Gearhead145/piled/Component Datasheets/PILED/113_0601/IMGP3079.JPG

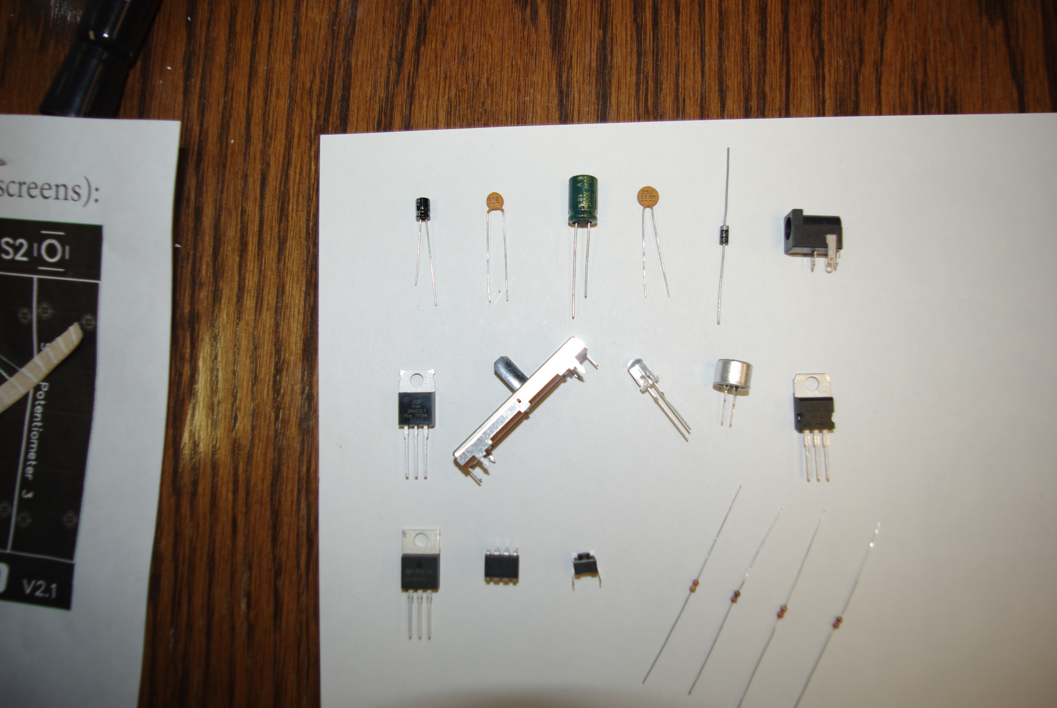
Component Datasheets/PILED/113_0601/IMGP3079.JPG
