Gearhead145/piled/Component Datasheets/PILED/113_0601/IMGP3086.JPG

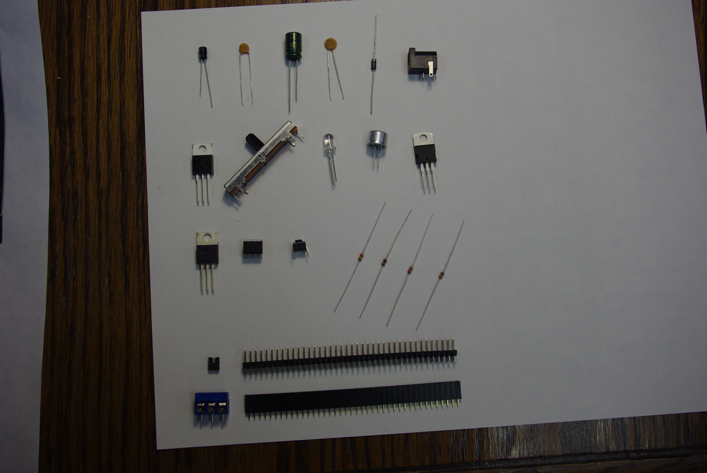
Component Datasheets/PILED/113_0601/IMGP3086.JPG
