Gearhead145/piled/Component Datasheets/PILED/113_0601/IMGP3090.JPG

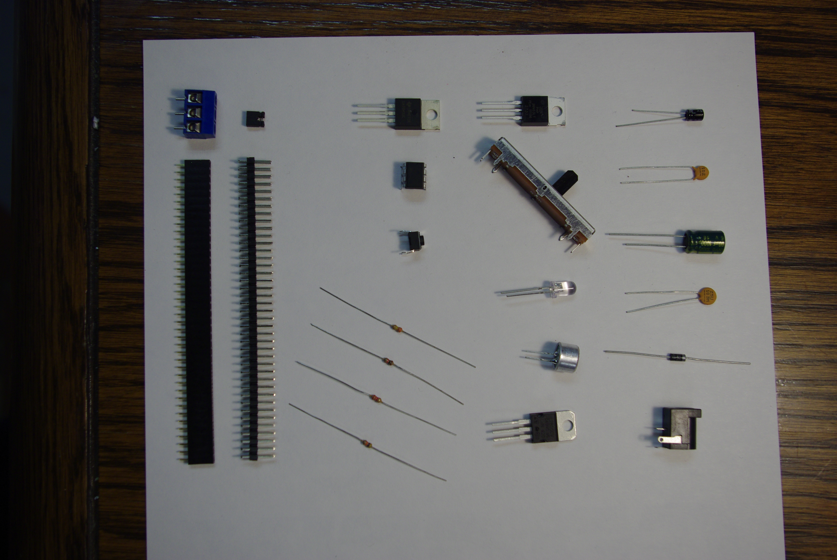
Component Datasheets/PILED/113_0601/IMGP3090.JPG
