Gearhead145/piled/Code/led_tile.h

/*
 * led_tile.h
 *
 *  Created on: Jun 10, 2012
 *      Author: Jorel Lalicki
 */

#ifndef LED_TILE_H_
#define LED_TILE_H_
#define period 4095 //period for PWM output

//Defines the on-board devices
#define F1 INCH_7
#define F2 INCH_5
#define F3 INCH_4
#define MIC INCH_0
#define S1 BIT3 //Port 1
#define S2 BIT0 //Port 2
#define R BIT6 //Port 1
#define G BIT1 //Port 2
#define B BIT4 //Port 2


char ADCDone;
int ADCValue;

//define three chars to keep track of linear representations of RGB values, prior to srgb conversion, to prevent the need to take sqrt.
char _r;
char _g;
char _b;




void init(void);
void set_lrgb(char r_new, char g_new, char b_new);
void set_rgb(char r_new, char g_new, char b_new);
void target_rgb(char r, char g, char  b, unsigned long time);
void sleed(int cycles);
int Single_Measure(unsigned int chan);
int _Single_Measure(unsigned int chan);


void sleep(int cycles){ //wastes cpu cycles in increments of 100 cycles, for software delays
	while (cycles>0){
		__delay_cycles(100);
		cycles-=100;
	}
}
void init(void){
	//set operating frequency to 16MHz
	DCOCTL = CALDCO_8MHZ;
	BCSCTL1 = CALBC1_8MHZ;

	//sets up the timer and sets ports to outputs/inputs
	WDTCTL = WDTPW + WDTHOLD;             // Stop watchdog timer
	P1DIR |= BIT6;// Set some pins to output direction

	//Set up Pin 1.3 as a button input
	P1DIR &= ~BIT3;
	P1REN |= BIT3;
	P1OUT |= BIT3;
	P1IE |= BIT3; // P1.3 interrupt enabled
	P1IFG &= ~BIT3; // P1.3 IFG cleared


	//******************************************

	//	  P1OUT |= BIT0+BIT1+BIT2+BIT3;

	P1DIR |= BIT6;             // P1.2 to output
	P1SEL |= BIT6;             // P1.2 to TA0.1
	P2DIR |= BIT1;             // P2.1 to output
	 P2SEL |= BIT1;             // P2.1 to TA1.1
	  P2DIR |= BIT4;             // P2.4 to output
	 P2SEL |= BIT4;             // P2.4 to TA1.2

 	  //*************************

 	//Set up timer
	CCTL1 = OUTMOD_7;                              // reset/set mode
	CCTL2 = OUTMOD_7;
	TA1CCTL1 = OUTMOD_7;
	TA1CCTL2 = OUTMOD_7;

	TACTL = TASSEL_2 + MC_1;           // SMCLK/8, upmode
	TA1CTL = TASSEL_2 + MC_1;

	CCR0 = period;        // period timer 0
	TA1CCR0 = period; //period timer 1
	CCR1 = 0;         // R
	CCR2 = 0;         // G
	_BIS_SR(GIE + TAIE); // Enable interrupts
	}


/*** Reads ADC 'chan' once using AVCC as the reference.**/
int _Single_Measure(unsigned int chan)
{
	ADC10CTL0 &= ~ENC;				// Disable ADC
	ADC10CTL0 = ADC10SHT_3 + ADC10ON + ADC10IE;	// 64 clock ticks, ADC On, enable ADC interrupt
	ADC10CTL1 = ADC10SSEL_3 + chan;				// Set 'chan', SMCLK
	ADC10CTL0 |= ENC + ADC10SC;             	// Enable and start conversion
	notdone:
	if(ADCDone==1)							// If the ADC is done with a measurement
			{
				ADCDone = 0;
				ADC10CTL0 |= ENC;				// Disable ADC

				return ADCValue;
			}
	else goto notdone;
}

int Single_Measure(unsigned int chan){
	return _Single_Measure(chan);// + _Single_Measure(chan) + _Single_Measure(chan) + _Single_Measure(chan) - 2) / 4; //take 4 readings, add them up and subtract 2 to take a true average
}



void target_rgb(char r, char g, char b, unsigned long time){


	//time is expected to be a multiple of 500
	unsigned long interval = time/500;
	float r_change =  _r;
	r_change -= r;
	r_change /= interval;

	float g_change =  _g;
	g_change -= g;
	g_change /= interval;

	float b_change =  _b;
	b_change -= b;
	b_change /= interval;

	//use existing values as a starting place - as floats, to allow very slow fading (change of <1 possible per iteration...)
	float r_temp = _r;
	float g_temp = _g;
	float b_temp = _b;


	long i;
	for(i = 0; i < interval; ++i){
			__delay_cycles(100);
			r_temp -= r_change;
			g_temp -= g_change;
			b_temp -= b_change;
			set_rgb(r_temp,g_temp,b_temp); //set the output to this intermediate color
	}
	//if all else failed, make sure the end result is right on target..., and update the internal linear values
	_r = r;
	_g = g;
	_b = b;
	set_rgb(r,g,b);
}



void set_lrgb(char r_new, char g_new, char b_new){ //linear RGB color space - not recommended for use!
	//update internal linear values
	_r = r_new;
	_g = g_new;
	_b = b_new;
	CCR1 = r_new*16;
	TA1CCR1 = g_new*16;
	TA1CCR2 = b_new*16;

}

void set_rgb(char r_new, char g_new, char b_new){ //non-linear colorspace: instantly set output color
	//update internal linear values
	_r = r_new;
	_g = g_new;
	_b = b_new;

	CCR1 = (float)((float)r_new / 255)*((float)r_new / 255)*4095;
	TA1CCR1 = (float)((float)g_new / 255)*((float)g_new / 255)*4095;
	TA1CCR2 = (float)((float)b_new / 255)*((float)b_new / 255)*4095;

}


/*** ADC interrupt routine. Pulls CPU out of sleep mode for the main loop.**/
#pragma vector=ADC10_VECTOR
__interrupt void ADC10_ISR (void)
{
	ADCValue = ADC10MEM;				// Saves measured value.
	ADCDone = 1;  					// Sets flag for main loop.
}

#endif /* LED_TILE_H_ */
