Gearhead145/piled/Code/launchpad_helpers.h

/*
 * launchpad_helpers.h
 *
 *  Created on: Jun 11, 2012
 *      Author: Jorel Lalicki
 */
#include <msp430.h>

#ifndef LAUNCHPAD_HELPERS_H_
#define LAUNCHPAD_HELPERS_H_





#endif /* LAUNCHPAD_HELPERS_H_ */
